ihatechoosingusernames/artseyio/artseyio-firmware/include/artseyio.c

#include "artseyio.h"
#include <usb_kbd.h>

// __code prefix stores this in code memory, so this array will be read only


// Brace Layer
__code const struct KeyLayer brace_layer = {
	.layer_mask = 0b10000000,	// Top left key held to activate
	.layer_size = 6,			// 6 keys in layer
	.layer_codes = {			// Output keys
		{
			.key_map = 0b01000000,
			.key_code = MOD_COMBINE(KEY_MOD_LSHIFT, KEY_9)
		},
		{
			.key_map = 0b00100000,
			.key_code = MOD_COMBINE(KEY_MOD_LSHIFT, KEY_0)
		},
		{
			.key_map = 0b00010000,
			.key_code = MOD_COMBINE(KEY_MOD_LSHIFT, KEY_LEFTBRACE)
		},
		{
			.key_map = 0b00000100,
			.key_code = KEY_LEFTBRACE
		},
		{
			.key_map = 0b00000010,
			.key_code = KEY_RIGHTBRACE
		},
		{
			.key_map = 0b00000001,
			.key_code = MOD_COMBINE(KEY_MOD_LSHIFT, KEY_RIGHTBRACE)
		}
	}
};

// Number Layer
__code const struct KeyLayer number_layer = {
	.layer_mask = 0b00010000,
	.layer_size = 10,
	.layer_codes = {
		{
			.key_map = 0b10000000,
			.key_code = KEY_1
		},
		{
			.key_map = 0b01000000,
			.key_code = KEY_2
		},
		{
			.key_map = 0b00100000,
			.key_code = KEY_3
		},
		{
			.key_map = 0b00001000,
			.key_code = KEY_4
		},
		{
			.key_map = 0b00000100,
			.key_code = KEY_5
		},
		{
			.key_map = 0b00000010,
			.key_code = KEY_6
		},
		{
			.key_map = 0b11000000,
			.key_code = KEY_7
		},
		{
			.key_map = 0b01100000,
			.key_code = KEY_8
		},
		{
			.key_map = 0b00001100,
			.key_code = KEY_9
		},
		{
			.key_map = 0b00000110,
			.key_code = KEY_0
		}
	},
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
	KEY_NONE,
	KEY_NONE,
	KEY_NONE,
	KEY_NONE,
	KEY_NONE,
	KEY_NONE,
	KEY_NONE,
	KEY_NONE,
	KEY_Q,		// 1011 0000
	KEY_NONE,
	KEY_NONE,
	KEY_NONE,
	KEY_NONE,
	KEY_NONE,
	KEY_NONE,
	KEY_NONE,
	KEY_NONE,
	KEY_NONE,
	KEY_NONE,
	KEY_NONE,
	KEY_NONE,
	KEY_NONE,
	KEY_NONE,
	KEY_NONE,
	KEY_F,		// 1100 0000
	KEY_ESC,	// 1100 0001
	KEY_NONE,
	KEY_NONE,
	KEY_NONE,
	KEY_NONE,
	KEY_NONE,
	KEY_NONE,
	KEY_NONE,
	KEY_NONE,
	KEY_NONE,
	KEY_NONE,
	KEY_NONE,
	KEY_NONE,
	KEY_NONE,
	KEY_NONE,
	KEY_NONE,
	KEY_NONE,
	KEY_NONE,
	KEY_NONE,
	KEY_NONE,
	KEY_NONE,
	KEY_NONE,
	KEY_NONE,
	KEY_NONE,
	KEY_NONE,
	KEY_NONE,
	KEY_NONE,
	KEY_NONE,
	KEY_NONE,
	KEY_NONE,
	KEY_NONE,
	KEY_D,		// 1110 0000
	KEY_TAB,	// 1110 0001
	KEY_NONE,
	KEY_NONE,
	KEY_NONE,
	KEY_NONE,
	KEY_NONE,
	KEY_NONE,
	KEY_NONE,
	KEY_NONE,
	KEY_NONE,
	KEY_NONE,
	KEY_NONE,
	KEY_NONE,
	KEY_NONE,
	KEY_NONE,
	KEY_Z		// 1111 0000
};

// Alternate hold functions
__code const struct KeyLayer* hold_layers[] = {
	&brace_layer,
	&number_layer,
	&symbol_layer,
	&custom_layer
};

__code const unsigned int hold_time = 300;	// How long in milliseconds constitutes holding vs tapping

uint8_t layer_state = 0;  	// This variable keeps track of the active layer
uint8_t prev_key_state = 0;	// The previous key state
uint8_t last_press = 0;		// The last key press that was handled

unsigned int hold_timer = 0;		// How long a key has been held for

void set_key_state(uint8_t key_state) {
	if ((key_state) && (prev_key_state == key_state)) {	// If a key is being held
		
		hold_timer += SCAN_DELAY;		// Update hold_timer

		if ((hold_timer > hold_time) && !layer_state)	// If key is held longer than timer, update
			hold_keys(key_state);

	// If keys are still being released from the last press
	} else if (last_press > key_state) {
		hold_timer = 0;
		last_press = key_state;

	// If a key has been released
	} else if (prev_key_state > key_state) {
		hold_timer = 0;					// Reset the hold timer

		// If the hold layer key has been released, only reset the layer state
		if ((layer_state | key_state) > key_state) {
			layer_state = 0;
		} else {
			tap_keys(prev_key_state);	// A key has been tapped
			last_press = key_state;
		}
	}

	prev_key_state = key_state;
}

void tap_keys(uint8_t key_state) {
	// Do a forward lookup for basic tap keys
	if (!layer_state) {
		// If tapped, use the tap key lookup
		press_key(tap_lookup[key_state]);
	// Do a reverse lookup for layered keys
	} else {
		// Look up the relevant layer
		for (uint8_t layer_index = 0; layer_index < NUM_LAYERS; layer_index++) {

			if (hold_layers[layer_index]->layer_mask == layer_state) {

				// Find the correct key in the layer
				for (uint8_t key_index = 0; key_index < hold_layers[layer_index]->layer_size; key_index++) {

					// Find the correct key combination
					if ((hold_layers[layer_index]->layer_codes[key_index].key_map | layer_state) == key_state) {
						press_key(hold_layers[layer_index]->layer_codes[key_index].key_code);
						return;
					}
				}
			}
		}
	}
}

void hold_keys(uint8_t key_state) {
	// Update the layer state mask if it is a valid layer
	for (uint8_t layer_index = 0; layer_index < NUM_LAYERS; layer_index++) {
		if (hold_layers[layer_index]->layer_mask == key_state)
			layer_state = key_state;
	}
}

void press_key(uint16_t key_code) {
	uint8_t out_key = GET_COMBINED_KEY(key_code);
	uint8_t out_mod = GET_COMBINED_MOD(key_code);

	KBD_mod_press(out_mod);

	// In case of oneshot mods, no report is sent and the mod waits until the next key press
	if (out_key) {
		KBD_type(out_key);
		KBD_mod_release_all();	// Release the given mod as well as any other oneshot mods
	}
}
